valuablelegend1-a11y/ARC-Insight/Code/firmware/sleep.h

#pragma once
#include <stdint.h>

namespace arcv {

enum class WakeReason : uint8_t {
  Unknown = 0,
  Comparator,
  Timer,
  PowerOn,
  Touch,
};

WakeReason wakeReason();
void enterDeepSleep(uint32_t guardSeconds);

}  // namespace arcv
